bemcgarvey/ATSAME51J20Demo/firmware/CDC/firmware/src/app.c

#include "app.h"
#include <string.h>

// *****************************************************************************
// *****************************************************************************
// Section: Global Data Definitions
// *****************************************************************************
// *****************************************************************************

uint8_t CACHE_ALIGN cdcReadBuffer[APP_READ_BUFFER_SIZE];
uint8_t CACHE_ALIGN cdcWriteBuffer[APP_READ_BUFFER_SIZE];


// *****************************************************************************
/* Application Data

  Summary:
    Holds application data

  Description:
    This structure holds the application's data.

  Remarks:
    This structure should be initialized by the APP_Initialize function.
    
    Application strings and buffers are be defined outside this structure.
 */

APP_DATA appData;


// *****************************************************************************
// *****************************************************************************
// Section: Application Callback Functions
// *****************************************************************************
// *****************************************************************************

/*******************************************************
 * USB CDC Device Events - Application Event Handler
 *******************************************************/

USB_DEVICE_CDC_EVENT_RESPONSE APP_USBDeviceCDCEventHandler
(
        USB_DEVICE_CDC_INDEX index,
        USB_DEVICE_CDC_EVENT event,
        void * pData,
        uintptr_t userData
        ) {
    APP_DATA * appDataObject;
    USB_CDC_CONTROL_LINE_STATE * controlLineStateData;
    USB_DEVICE_CDC_EVENT_DATA_READ_COMPLETE * eventDataRead;

    appDataObject = (APP_DATA *) userData;

    switch (event) {
        case USB_DEVICE_CDC_EVENT_GET_LINE_CODING:

            /* This means the host wants to know the current line
             * coding. This is a control transfer request. Use the
             * USB_DEVICE_ControlSend() function to send the data to
             * host.  */

            USB_DEVICE_ControlSend(appDataObject->deviceHandle,
                    &appDataObject->getLineCodingData, sizeof (USB_CDC_LINE_CODING));

            break;

        case USB_DEVICE_CDC_EVENT_SET_LINE_CODING:

            /* This means the host wants to set the line coding.
             * This is a control transfer request. Use the
             * USB_DEVICE_ControlReceive() function to receive the
             * data from the host */

            USB_DEVICE_ControlReceive(appDataObject->deviceHandle,
                    &appDataObject->setLineCodingData, sizeof (USB_CDC_LINE_CODING));

            break;

        case USB_DEVICE_CDC_EVENT_SET_CONTROL_LINE_STATE:

            /* This means the host is setting the control line state.
             * Read the control line state. We will accept this request
             * for now. */

            controlLineStateData = (USB_CDC_CONTROL_LINE_STATE *) pData;
            appDataObject->controlLineStateData.dtr = controlLineStateData->dtr;
            appDataObject->controlLineStateData.carrier = controlLineStateData->carrier;

            USB_DEVICE_ControlStatus(appDataObject->deviceHandle, USB_DEVICE_CONTROL_STATUS_OK);

            break;

        case USB_DEVICE_CDC_EVENT_SEND_BREAK:

            /* This means that the host is requesting that a break of the
             * specified duration be sent. Read the break duration */

            appDataObject->breakData = ((USB_DEVICE_CDC_EVENT_DATA_SEND_BREAK *) pData)->breakDuration;

            /* Complete the control transfer by sending a ZLP  */
            USB_DEVICE_ControlStatus(appDataObject->deviceHandle, USB_DEVICE_CONTROL_STATUS_OK);

            break;

        case USB_DEVICE_CDC_EVENT_READ_COMPLETE:

            /* This means that the host has sent some data*/
            eventDataRead = (USB_DEVICE_CDC_EVENT_DATA_READ_COMPLETE *) pData;

            if (eventDataRead->status != USB_DEVICE_CDC_RESULT_ERROR) {
                appDataObject->isReadComplete = true;

                appDataObject->numBytesRead = eventDataRead->length;
            }
            break;

        case USB_DEVICE_CDC_EVENT_CONTROL_TRANSFER_DATA_RECEIVED:

            /* The data stage of the last control transfer is
             * complete. For now we accept all the data */

            USB_DEVICE_ControlStatus(appDataObject->deviceHandle, USB_DEVICE_CONTROL_STATUS_OK);
            break;

        case USB_DEVICE_CDC_EVENT_CONTROL_TRANSFER_DATA_SENT:

            /* This means the GET LINE CODING function data is valid. We don't
             * do much with this data in this demo. */
            break;

        case USB_DEVICE_CDC_EVENT_WRITE_COMPLETE:

            /* This means that the data write got completed. We can schedule
             * the next read. */

            appDataObject->isWriteComplete = true;
            break;

        default:
            break;
    }

    return USB_DEVICE_CDC_EVENT_RESPONSE_NONE;
}

/***********************************************
 * Application USB Device Layer Event Handler.
 ***********************************************/
void APP_USBDeviceEventHandler
(
        USB_DEVICE_EVENT event,
        void * eventData,
        uintptr_t context
        ) {
    USB_DEVICE_EVENT_DATA_CONFIGURED *configuredEventData;

    switch (event) {
        case USB_DEVICE_EVENT_SOF:

            /* This event is used for switch debounce. This flag is reset
             * by the switch process routine. */
            appData.sofEventHasOccurred = true;

            break;

        case USB_DEVICE_EVENT_RESET:

            /* Update LED to show reset state */
            LED_Off();

            appData.isConfigured = false;

            break;

        case USB_DEVICE_EVENT_CONFIGURED:

            /* Check the configuration. We only support configuration 1 */
            configuredEventData = (USB_DEVICE_EVENT_DATA_CONFIGURED*) eventData;

            if (configuredEventData->configurationValue == 1) {
                /* Update LED to show configured state */
                LED_On();

                /* Register the CDC Device application event handler here.
                 * Note how the appData object pointer is passed as the
                 * user data */

                USB_DEVICE_CDC_EventHandlerSet(USB_DEVICE_CDC_INDEX_0, APP_USBDeviceCDCEventHandler, (uintptr_t) & appData);

                /* Mark that the device is now configured */
                appData.isConfigured = true;
            }

            break;

        case USB_DEVICE_EVENT_POWER_DETECTED:

            /* VBUS was detected. We can attach the device */
            USB_DEVICE_Attach(appData.deviceHandle);

            break;

        case USB_DEVICE_EVENT_POWER_REMOVED:

            /* VBUS is not available. We can detach the device */
            USB_DEVICE_Detach(appData.deviceHandle);

            appData.isConfigured = false;

            LED_Off();

            break;

        case USB_DEVICE_EVENT_SUSPENDED:

            /* Switch LED to show suspended state */
            LED_Off();

            break;

        case USB_DEVICE_EVENT_RESUMED:
        case USB_DEVICE_EVENT_ERROR:
        default:

            break;
    }
}

// *****************************************************************************
// *****************************************************************************
// Section: Application Local Functions
// *****************************************************************************
// *****************************************************************************

/*****************************************************
 * This function is called in every step of the
 * application state machine.
 *****************************************************/

bool APP_StateReset(void) {
    /* This function returns true if the device
     * was reset  */

    bool retVal;

    if (appData.isConfigured == false) {
        appData.state = APP_STATE_WAIT_FOR_CONFIGURATION;
        appData.readTransferHandle = USB_DEVICE_CDC_TRANSFER_HANDLE_INVALID;
        appData.writeTransferHandle = USB_DEVICE_CDC_TRANSFER_HANDLE_INVALID;
        appData.isReadComplete = true;
        appData.isWriteComplete = true;
        retVal = true;
    } else {
        retVal = false;
    }

    return (retVal);
}

// *****************************************************************************
// *****************************************************************************
// Section: Application Initialization and State Machine Functions
// *****************************************************************************
// *****************************************************************************

/*******************************************************************************
  Function:
    void APP_Initialize(void)

  Remarks:
    See prototype in app.h.
 */

void APP_Initialize(void) {
    /* Place the App state machine in its initial state. */
    appData.state = APP_STATE_INIT;

    /* Device Layer Handle  */
    appData.deviceHandle = USB_DEVICE_HANDLE_INVALID;

    /* Device configured status */
    appData.isConfigured = false;

    /* Initial get line coding state */
    appData.getLineCodingData.dwDTERate = 9600;
    appData.getLineCodingData.bParityType = 0;
    appData.getLineCodingData.bParityType = 0;
    appData.getLineCodingData.bDataBits = 8;

    /* Read Transfer Handle */
    appData.readTransferHandle = USB_DEVICE_CDC_TRANSFER_HANDLE_INVALID;

    /* Write Transfer Handle */
    appData.writeTransferHandle = USB_DEVICE_CDC_TRANSFER_HANDLE_INVALID;

    /* Initialize the read complete flag */
    appData.isReadComplete = true;

    /*Initialize the write complete flag*/
    appData.isWriteComplete = true;

    /* Reset other flags */
    appData.sofEventHasOccurred = false;

    /* Set up the read buffer */
    appData.cdcReadBuffer = &cdcReadBuffer[0];

    /* Set up the read buffer */
    appData.cdcWriteBuffer = &cdcWriteBuffer[0];
}

/******************************************************************************
  Function:
    void APP_Tasks(void)

  Remarks:
    See prototype in app.h.
 */

void APP_Tasks(void) {
    /* Update the application state machine based
     * on the current state */

    switch (appData.state) {
        case APP_STATE_INIT:

            /* Open the device layer */
            appData.deviceHandle = USB_DEVICE_Open(USB_DEVICE_INDEX_0, DRV_IO_INTENT_READWRITE);

            if (appData.deviceHandle != USB_DEVICE_HANDLE_INVALID) {
                /* Register a callback with device layer to get event notification (for end point 0) */
                USB_DEVICE_EventHandlerSet(appData.deviceHandle, APP_USBDeviceEventHandler, 0);

                appData.state = APP_STATE_WAIT_FOR_CONFIGURATION;
            } else {
                /* The Device Layer is not ready to be opened. We should try
                 * again later. */
            }

            break;

        case APP_STATE_WAIT_FOR_CONFIGURATION:

            /* Check if the device was configured */
            if (appData.isConfigured) {
                /* If the device is configured then lets start reading */
                appData.state = APP_STATE_SCHEDULE_READ;
            }

            break;

        case APP_STATE_SCHEDULE_READ:

            if (APP_StateReset()) {
                break;
            }

            /* If a read is complete, then schedule a read
             * else wait for the current read to complete */

            appData.state = APP_STATE_WAIT_FOR_READ_COMPLETE;
            if (appData.isReadComplete == true) {
                appData.isReadComplete = false;
                appData.readTransferHandle = USB_DEVICE_CDC_TRANSFER_HANDLE_INVALID;

                USB_DEVICE_CDC_Read(USB_DEVICE_CDC_INDEX_0,
                        &appData.readTransferHandle, appData.cdcReadBuffer,
                        APP_READ_BUFFER_SIZE);

                if (appData.readTransferHandle == USB_DEVICE_CDC_TRANSFER_HANDLE_INVALID) {
                    appData.state = APP_STATE_ERROR;
                    break;
                }
            }

            break;

        case APP_STATE_WAIT_FOR_READ_COMPLETE:
            if (APP_StateReset()) {
                break;
            }
            if (appData.isReadComplete) {
                for (int i = 0; i < appData.numBytesRead; ++i) {
                    while (appData.isWriteComplete == false) {
                        vTaskDelay(1);
                    }
                    appData.numBytesToWrite = 0;
                    switch (appData.cdcReadBuffer[i]) {
                        case '1': BlueLed_Toggle();
                            break;
                        case '2': GreenLed_Set();
                            strcpy((char *) appData.cdcWriteBuffer, "Green On\r\n");
                            appData.numBytesToWrite = strlen((char *) appData.cdcWriteBuffer);
                            break;
                        case '3': GreenLed_Clear();
                            strcpy((char *) appData.cdcWriteBuffer, "Green Off\r\n");
                            appData.numBytesToWrite = strlen((char *) appData.cdcWriteBuffer);
                            break;
                        case '4':
                            for (int j = 0; j < 26 * 4; ++j) {
                                appData.cdcWriteBuffer[j] = 'a' + (j % 26);
                            }
                            appData.cdcWriteBuffer[26 * 4] = '\r';
                            appData.cdcWriteBuffer[26 * 4 + 1] = '\n';
                            appData.cdcWriteBuffer[26 * 4 + 2] = '\0';
                            appData.numBytesToWrite = strlen((char *) appData.cdcWriteBuffer);
                            break;
                    }
                    if (appData.numBytesToWrite > 0) {
                        appData.writeTransferHandle = USB_DEVICE_CDC_TRANSFER_HANDLE_INVALID;
                        appData.isWriteComplete = false;
                        appData.state = APP_STATE_WAIT_FOR_WRITE_COMPLETE;
                        USB_DEVICE_CDC_Write(USB_DEVICE_CDC_INDEX_0,
                                &appData.writeTransferHandle,
                                appData.cdcWriteBuffer, appData.numBytesToWrite,
                                USB_DEVICE_CDC_TRANSFER_FLAGS_DATA_COMPLETE);
                    }
                }
                appData.state = APP_STATE_SCHEDULE_READ;
            }
            break;
        case APP_STATE_SCHEDULE_WRITE:

            if (APP_StateReset()) {
                break;
            }
            /* Setup the write */
            appData.writeTransferHandle = USB_DEVICE_CDC_TRANSFER_HANDLE_INVALID;
            appData.isWriteComplete = false;
            appData.state = APP_STATE_WAIT_FOR_WRITE_COMPLETE;
            USB_DEVICE_CDC_Write(USB_DEVICE_CDC_INDEX_0,
                    &appData.writeTransferHandle,
                    appData.cdcWriteBuffer, appData.numBytesToWrite,
                    USB_DEVICE_CDC_TRANSFER_FLAGS_DATA_COMPLETE);
            break;
        case APP_STATE_WAIT_FOR_WRITE_COMPLETE:
            if (APP_StateReset()) {
                break;
            }
            if (appData.isWriteComplete == true) {
                appData.state = APP_STATE_SCHEDULE_READ;
            }
            break;
        case APP_STATE_ERROR:
        default:
            break;
    }
}

/*******************************************************************************
 End of File
 */
