bemcgarvey/ATSAME51J20Demo/firmware/CDC/firmware/src/config/default/initialization.c

/*******************************************************************************
  System Initialization File

  File Name:
    initialization.c

  Summary:
    This file contains source code necessary to initialize the system.

  Description:
    This file contains source code necessary to initialize the system.  It
    implements the "SYS_Initialize" function, defines the configuration bits,
    and allocates any necessary global system resources,
 *******************************************************************************/

// DOM-IGNORE-BEGIN
/*******************************************************************************
* Copyright (C) 2018 Microchip Technology Inc. and its subsidiaries.
*
* Subject to your compliance with these terms, you may use Microchip software
* and any derivatives exclusively with Microchip products. It is your
* responsibility to comply with third party license terms applicable to your
* use of third party software (including open source software) that may
* accompany Microchip software.
*
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
* IN NO EVENT WILL MICROCHIP BE LIABLE FOR ANY INDIRECT, SPECIAL, PUNITIVE,
* INCIDENTAL OR CONSEQUENTIAL LOSS, DAMAGE, COST OR EXPENSE OF ANY KIND
* WHATSOEVER RELATED TO THE SOFTWARE, HOWEVER CAUSED, EVEN IF MICROCHIP HAS
* BEEN ADVISED OF THE POSSIBILITY OR THE DAMAGES ARE FORESEEABLE. TO THE
* FULLEST EXTENT ALLOWED BY LAW, MICROCHIP'S TOTAL LIABILITY ON ALL CLAIMS IN
* ANY WAY RELATED TO THIS SOFTWARE WILL NOT EXCEED THE AMOUNT OF FEES, IF ANY,
* THAT YOU HAVE PAID DIRECTLY TO MICROCHIP FOR THIS SOFTWARE.
 *******************************************************************************/
// DOM-IGNORE-END

// *****************************************************************************
// *****************************************************************************
// Section: Included Files
// *****************************************************************************
// *****************************************************************************
#include "configuration.h"
#include "definitions.h"
#include "device.h"



// ****************************************************************************
// ****************************************************************************
// Section: Configuration Bits
// ****************************************************************************
// ****************************************************************************
#pragma config BOD33_DIS = SET
#pragma config BOD33USERLEVEL = 0x1c
#pragma config BOD33_ACTION = RESET
#pragma config BOD33_HYST = 0x2
#pragma config NVMCTRL_BOOTPROT = 0
#pragma config NVMCTRL_SEESBLK = 0x0
#pragma config NVMCTRL_SEEPSZ = 0x0
#pragma config RAMECC_ECCDIS = SET
#pragma config WDT_ENABLE = CLEAR
#pragma config WDT_ALWAYSON = CLEAR
#pragma config WDT_PER = CYC8192
#pragma config WDT_WINDOW = CYC8192
#pragma config WDT_EWOFFSET = CYC8192
#pragma config WDT_WEN = CLEAR
#pragma config NVMCTRL_REGION_LOCKS = 0xffffffff




// *****************************************************************************
// *****************************************************************************
// Section: Driver Initialization Data
// *****************************************************************************
// *****************************************************************************
// <editor-fold defaultstate="collapsed" desc="DRV_SDMMC Instance 0 Initialization Data">

/* SDMMC Client Objects Pool */
static DRV_SDMMC_CLIENT_OBJ drvSDMMC0ClientObjPool[DRV_SDMMC_CLIENTS_NUMBER_IDX0];

/* SDMMC Transfer Objects Pool */
static DRV_SDMMC_BUFFER_OBJ drvSDMMC0BufferObjPool[DRV_SDMMC_QUEUE_SIZE_IDX0];


const DRV_SDMMC_PLIB_API drvSDMMC0PlibAPI = {
    .sdhostCallbackRegister = (DRV_SDMMC_PLIB_CALLBACK_REGISTER)SDHC0_CallbackRegister,
    .sdhostInitModule = (DRV_SDMMC_PLIB_INIT_MODULE)SDHC0_ModuleInit,
    .sdhostSetClock  = (DRV_SDMMC_PLIB_SET_CLOCK)SDHC0_ClockSet,
    .sdhostIsCmdLineBusy = (DRV_SDMMC_PLIB_IS_CMD_LINE_BUSY)SDHC0_IsCmdLineBusy,
    .sdhostIsDatLineBusy = (DRV_SDMMC_PLIB_IS_DATA_LINE_BUSY)SDHC0_IsDatLineBusy,
    .sdhostSendCommand = (DRV_SDMMC_PLIB_SEND_COMMAND)SDHC0_CommandSend,
    .sdhostReadResponse = (DRV_SDMMC_PLIB_READ_RESPONSE)SDHC0_ResponseRead,
    .sdhostSetBlockCount = (DRV_SDMMC_PLIB_SET_BLOCK_COUNT)SDHC0_BlockCountSet,
    .sdhostSetBlockSize = (DRV_SDMMC_PLIB_SET_BLOCK_SIZE)SDHC0_BlockSizeSet,
    .sdhostSetBusWidth = (DRV_SDMMC_PLIB_SET_BUS_WIDTH)SDHC0_BusWidthSet,
    .sdhostSetSpeedMode = (DRV_SDMMC_PLIB_SET_SPEED_MODE)SDHC0_SpeedModeSet,
    .sdhostSetupDma = (DRV_SDMMC_PLIB_SETUP_DMA)SDHC0_DmaSetup,
    .sdhostGetCommandError = (DRV_SDMMC_PLIB_GET_COMMAND_ERROR)SDHC0_CommandErrorGet,
    .sdhostGetDataError = (DRV_SDMMC_PLIB_GET_DATA_ERROR)SDHC0_DataErrorGet,
    .sdhostClockEnable = (DRV_SDMMC_PLIB_CLOCK_ENABLE)SDHC0_ClockEnable,
    .sdhostResetError = (DRV_SDMMC_PLIB_RESET_ERROR)SDHC0_ErrorReset,
    .sdhostIsCardAttached = (DRV_SDMMC_PLIB_IS_CARD_ATTACHED)SDHC0_IsCardAttached,
    .sdhostIsWriteProtected = (DRV_SDMMC_PLIB_IS_WRITE_PROTECTED)NULL,
};

/*** SDMMC Driver Initialization Data ***/
const DRV_SDMMC_INIT drvSDMMC0InitData =
{
    .sdmmcPlib                      = &drvSDMMC0PlibAPI,
    .bufferObjPool                  = (uintptr_t)&drvSDMMC0BufferObjPool[0],
    .bufferObjPoolSize              = DRV_SDMMC_QUEUE_SIZE_IDX0,
    .clientObjPool                  = (uintptr_t)&drvSDMMC0ClientObjPool[0],
    .numClients                     = DRV_SDMMC_CLIENTS_NUMBER_IDX0,
    .protocol                       = DRV_SDMMC_PROTOCOL_SUPPORT_IDX0,
    .cardDetectionMethod            = DRV_SDMMC_CARD_DETECTION_METHOD_IDX0,
    .cardDetectionPollingIntervalMs = 0,
    .isWriteProtectCheckEnabled     = false,
    .speedMode                      = DRV_SDMMC_CONFIG_SPEED_MODE_IDX0,
    .busWidth                       = DRV_SDMMC_CONFIG_BUS_WIDTH_IDX0,
	.sleepWhenIdle 					= false,
    .isFsEnabled                    = false,
};

// </editor-fold>



// *****************************************************************************
// *****************************************************************************
// Section: System Data
// *****************************************************************************
// *****************************************************************************
/* Structure to hold the object handles for the modules in the system. */
SYSTEM_OBJECTS sysObj;

// *****************************************************************************
// *****************************************************************************
// Section: Library/Stack Initialization Data
// *****************************************************************************
// *****************************************************************************
/******************************************************
 * USB Driver Initialization
 ******************************************************/
 
/*  When designing a Self-powered USB Device, the application should make sure
    that USB_DEVICE_Attach() function is called only when VBUS is actively powered.
	Therefore, the firmware needs some means to detect when the Host is powering 
	the VBUS. A 5V tolerant I/O pin can be connected to VBUS (through a resistor)
	and can be used to detect when VBUS is high or low. The application can specify
	a VBUS Detect function through the USB Driver Initialize data structure. 
	The USB device stack will periodically call this function. If the VBUS is 
	detected, the USB_DEVICE_EVENT_POWER_DETECTED event is generated. If the VBUS 
	is removed (i.e., the device is physically detached from Host), the USB stack 
	will generate the event USB_DEVICE_EVENT_POWER_REMOVED. The application should 
	call USB_DEVICE_Detach() when VBUS is removed. 
    
    The following are the steps to generate the VBUS_SENSE Function through MHC     
        1) Navigate to MHC->Tools->Pin Configuration and Configure the pin used 
		   as VBUS_SENSE. Set this pin Function as "GPIO" and set as "Input". 
		   Provide a custom name to the pin.
        2) Select the USB Driver Component in MHC Project Graph and enable the  
		   "Enable VBUS Sense" Check-box.     
        3) Specify the custom name of the VBUS SENSE pin in the "VBUS SENSE Pin Name" box.  */ 
static DRV_USB_VBUS_LEVEL DRV_USBFSV1_VBUS_Comparator(void)
{
    DRV_USB_VBUS_LEVEL retVal = DRV_USB_VBUS_LEVEL_INVALID;
    
    if(true == USB_VBUS_SENSE_Get())
    {
        retVal = DRV_USB_VBUS_LEVEL_VALID;
    }
	return (retVal);

}


const DRV_USBFSV1_INIT drvUSBInit =
{
	/* Interrupt Source for USB module */
	.interruptSource = USB_OTHER_IRQn,
 
	/* Interrupt Source for USB module */
	.interruptSource1 = USB_SOF_HSOF_IRQn,
 
	/* Interrupt Source for USB module */
	.interruptSource2 = USB_TRCPT0_IRQn,
 
	/* Interrupt Source for USB module */
	.interruptSource3 = USB_TRCPT1_IRQn,

    /* System module initialization */
    .moduleInit = {0},

    /* USB Controller to operate as USB Device */
    .operationMode = DRV_USBFSV1_OPMODE_DEVICE,

    /* USB Full Speed Operation */
	.operationSpeed = USB_SPEED_FULL,
    
    /* Stop in idle */
    .runInStandby = true,

    /* Suspend in sleep */
    .suspendInSleep = false,

    /* Identifies peripheral (PLIB-level) ID */
    .usbID = USB_REGS,
	
    /* Function to check for VBus */
    .vbusComparator = DRV_USBFSV1_VBUS_Comparator
	
};




// *****************************************************************************
// *****************************************************************************
// Section: System Initialization
// *****************************************************************************
// *****************************************************************************
// <editor-fold defaultstate="collapsed" desc="SYS_TIME Initialization Data">

const SYS_TIME_PLIB_INTERFACE sysTimePlibAPI = {
    .timerCallbackSet = (SYS_TIME_PLIB_CALLBACK_REGISTER)TC0_TimerCallbackRegister,
    .timerStart = (SYS_TIME_PLIB_START)TC0_TimerStart,
    .timerStop = (SYS_TIME_PLIB_STOP)TC0_TimerStop,
    .timerFrequencyGet = (SYS_TIME_PLIB_FREQUENCY_GET)TC0_TimerFrequencyGet,
    .timerPeriodSet = (SYS_TIME_PLIB_PERIOD_SET)TC0_Timer16bitPeriodSet,
    .timerCompareSet = (SYS_TIME_PLIB_COMPARE_SET)TC0_Timer16bitCompareSet,
    .timerCounterGet = (SYS_TIME_PLIB_COUNTER_GET)TC0_Timer16bitCounterGet,
};

const SYS_TIME_INIT sysTimeInitData =
{
    .timePlib = &sysTimePlibAPI,
    .hwTimerIntNum = TC0_IRQn,
};

// </editor-fold>



// *****************************************************************************
// *****************************************************************************
// Section: Local initialization functions
// *****************************************************************************
// *****************************************************************************



/*******************************************************************************
  Function:
    void SYS_Initialize ( void *data )

  Summary:
    Initializes the board, services, drivers, application and other modules.

  Remarks:
 */

void SYS_Initialize ( void* data )
{

    NVMCTRL_Initialize( );

  
    PORT_Initialize();

    CLOCK_Initialize();




    EVSYS_Initialize();

    TC0_TimerInitialize();

	SDHC0_Initialize();



    sysObj.drvSDMMC0 = DRV_SDMMC_Initialize(DRV_SDMMC_INDEX_0,(SYS_MODULE_INIT *)&drvSDMMC0InitData);


    sysObj.sysTime = SYS_TIME_Initialize(SYS_TIME_INDEX_0, (SYS_MODULE_INIT *)&sysTimeInitData);


	 /* Initialize the USB device layer */
    sysObj.usbDevObject0 = USB_DEVICE_Initialize (USB_DEVICE_INDEX_0 , ( SYS_MODULE_INIT* ) & usbDevInitData);
	
	

	/* Initialize USB Driver */ 
    sysObj.drvUSBFSV1Object = DRV_USBFSV1_Initialize(DRV_USBFSV1_INDEX_0, (SYS_MODULE_INIT *) &drvUSBInit);	


    APP_Initialize();


    NVIC_Initialize();

}


/*******************************************************************************
 End of File
*/
