bemcgarvey/ATSAME51J20Demo/firmware/Demo/firmware/src/config/default/peripheral/sercom/i2c_master/plib_sercom1_i2c_master.c

/*******************************************************************************
  Serial Communication Interface Inter-Integrated Circuit (SERCOM I2C) Library
  Source File

  Company:
    Microchip Technology Inc.

  File Name:
    plib_sercom1_i2c.c

  Summary:
    SERCOM I2C PLIB Implementation file

  Description:
    This file defines the interface to the SERCOM I2C peripheral library.
    This library provides access to and control of the associated peripheral
    instance.

*******************************************************************************/
// DOM-IGNORE-BEGIN
/*******************************************************************************
* Copyright (C) 2018 Microchip Technology Inc. and its subsidiaries.
*
* Subject to your compliance with these terms, you may use Microchip software
* and any derivatives exclusively with Microchip products. It is your
* responsibility to comply with third party license terms applicable to your
* use of third party software (including open source software) that may
* accompany Microchip software.
*
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
* IN NO EVENT WILL MICROCHIP BE LIABLE FOR ANY INDIRECT, SPECIAL, PUNITIVE,
* INCIDENTAL OR CONSEQUENTIAL LOSS, DAMAGE, COST OR EXPENSE OF ANY KIND
* WHATSOEVER RELATED TO THE SOFTWARE, HOWEVER CAUSED, EVEN IF MICROCHIP HAS
* BEEN ADVISED OF THE POSSIBILITY OR THE DAMAGES ARE FORESEEABLE. TO THE
* FULLEST EXTENT ALLOWED BY LAW, MICROCHIP'S TOTAL LIABILITY ON ALL CLAIMS IN
* ANY WAY RELATED TO THIS SOFTWARE WILL NOT EXCEED THE AMOUNT OF FEES, IF ANY,
* THAT YOU HAVE PAID DIRECTLY TO MICROCHIP FOR THIS SOFTWARE.
*******************************************************************************/
// DOM-IGNORE-END

// *****************************************************************************
// *****************************************************************************
// Section: Included Files
// *****************************************************************************
// *****************************************************************************

#include "interrupts.h"
#include "plib_sercom1_i2c_master.h"


// *****************************************************************************
// *****************************************************************************
// Section: Global Data
// *****************************************************************************
// *****************************************************************************


#define SERCOM1_I2CM_SPEED_HZ           100000

/* SERCOM1 I2C baud value */
#define SERCOM1_I2CM_BAUD_VALUE         (0xFFU)


static SERCOM_I2C_OBJ sercom1I2CObj;

// *****************************************************************************
// *****************************************************************************
// Section: SERCOM1 I2C Implementation
// *****************************************************************************
// *****************************************************************************
// *****************************************************************************

void SERCOM1_I2C_Initialize(void)
{
    /* Reset the module */
    SERCOM1_REGS->I2CM.SERCOM_CTRLA = SERCOM_I2CM_CTRLA_SWRST_Msk ;

    /* Wait for synchronization */
    while((SERCOM1_REGS->I2CM.SERCOM_SYNCBUSY) != 0U)
    {
        /* Do nothing */
    }

    /* Enable smart mode */
    SERCOM1_REGS->I2CM.SERCOM_CTRLB = SERCOM_I2CM_CTRLB_SMEN_Msk;

    /* Wait for synchronization */
    while((SERCOM1_REGS->I2CM.SERCOM_SYNCBUSY) != 0U)
    {
        /* Do nothing */
    }

    /* Baud rate - Master Baud Rate*/
    SERCOM1_REGS->I2CM.SERCOM_BAUD = SERCOM1_I2CM_BAUD_VALUE;

    /* Set Operation Mode (Master), SDA Hold time, run in stand by and i2c master enable */
    SERCOM1_REGS->I2CM.SERCOM_CTRLA = SERCOM_I2CM_CTRLA_MODE_I2C_MASTER | SERCOM_I2CM_CTRLA_SDAHOLD_75NS | SERCOM_I2CM_CTRLA_SPEED_STANDARD_AND_FAST_MODE | SERCOM_I2CM_CTRLA_SCLSM(0UL) | SERCOM_I2CM_CTRLA_ENABLE_Msk ;

    /* Wait for synchronization */
    while((SERCOM1_REGS->I2CM.SERCOM_SYNCBUSY) != 0U)
    {
        /* Do nothing */
    }

    /* Initial Bus State: IDLE */
    SERCOM1_REGS->I2CM.SERCOM_STATUS = (uint16_t)SERCOM_I2CM_STATUS_BUSSTATE(0x01UL);

    /* Wait for synchronization */
    while((SERCOM1_REGS->I2CM.SERCOM_SYNCBUSY) != 0U)
    {
        /* Do nothing */
    }

    /* Initialize the SERCOM1 PLib Object */
    sercom1I2CObj.error = SERCOM_I2C_ERROR_NONE;
    sercom1I2CObj.state = SERCOM_I2C_STATE_IDLE;

    /* Enable all Interrupts */
    SERCOM1_REGS->I2CM.SERCOM_INTENSET = (uint8_t)SERCOM_I2CM_INTENSET_Msk;
}

static bool SERCOM1_I2C_CalculateBaudValue(uint32_t srcClkFreq, uint32_t i2cClkSpeed, uint32_t* baudVal)
{
    uint32_t baudValue = 0U;
    float fSrcClkFreq = (float)srcClkFreq;
    float fI2cClkSpeed = (float)i2cClkSpeed;
    float fBaudValue = 0.0f;

    /* Reference clock frequency must be atleast two times the baud rate */
    if (srcClkFreq < (2U * i2cClkSpeed))
    {
        return false;
    }

    if (i2cClkSpeed <= 1000000U)
    {
        /* Standard, FM and FM+ baud calculation */
        fBaudValue = (fSrcClkFreq / fI2cClkSpeed) - ((fSrcClkFreq * (100.0f / 1000000000.0f)) + 10.0f);
        baudValue = (uint32_t)fBaudValue;
    }
    else
    {
        return false;
    }
    if (i2cClkSpeed <= 400000U)
    {
        /* For I2C clock speed upto 400 kHz, the value of BAUD<7:0> determines both SCL_L and SCL_H with SCL_L = SCL_H */
        if (baudValue > (0xFFU * 2U))
        {
            /* Set baud rate to the minimum possible value */
            baudValue = 0xFFU;
        }
        else if (baudValue <= 1U)
        {
            /* Baud value cannot be 0. Set baud rate to maximum possible value */
            baudValue = 1U;
        }
        else
        {
            baudValue /= 2U;
        }
    }
    else
    {
        /* To maintain the ratio of SCL_L:SCL_H to 2:1, the max value of BAUD_LOW<15:8>:BAUD<7:0> can be 0xFF:0x7F. Hence BAUD_LOW + BAUD can not exceed 255+127 = 382 */
        if (baudValue >= 382U)
        {
            /* Set baud rate to the minimum possible value while maintaining SCL_L:SCL_H to 2:1 */
            baudValue = (0xFFUL << 8U) | (0x7FU);
        }
        else if (baudValue <= 3U)
        {
            /* Baud value cannot be 0. Set baud rate to maximum possible value while maintaining SCL_L:SCL_H to 2:1 */
            baudValue = (2UL << 8U) | 1U;
        }
        else
        {
            /* For Fm+ mode, I2C SCL_L:SCL_H to 2:1 */
            baudValue  = ((((baudValue * 2U)/3U) << 8U) | (baudValue/3U));
        }
    }
    *baudVal = baudValue;
    return true;
}

bool SERCOM1_I2C_TransferSetup(SERCOM_I2C_TRANSFER_SETUP* setup, uint32_t srcClkFreq )
{
    uint32_t baudValue;
    uint32_t i2cClkSpeed;
    uint32_t i2cSpeedMode = 0;

    if (setup == NULL)
    {
        return false;
    }

    i2cClkSpeed = setup->clkSpeed;

    if( srcClkFreq == 0U)
    {
        srcClkFreq = 60000000UL;
    }

    if (SERCOM1_I2C_CalculateBaudValue(srcClkFreq, i2cClkSpeed, &baudValue) == false)
    {
        return false;
    }

    if (i2cClkSpeed > 400000U)
    {
        i2cSpeedMode = 1U;
    }

    /* Disable the I2C before changing the I2C clock speed */
    SERCOM1_REGS->I2CM.SERCOM_CTRLA &= ~SERCOM_I2CM_CTRLA_ENABLE_Msk;

    /* Wait for synchronization */
    while((SERCOM1_REGS->I2CM.SERCOM_SYNCBUSY) != 0U)
    {
        /* Do nothing */
    }


    /* Baud rate - Master Baud Rate*/
    SERCOM1_REGS->I2CM.SERCOM_BAUD = baudValue;

    SERCOM1_REGS->I2CM.SERCOM_CTRLA  = ((SERCOM1_REGS->I2CM.SERCOM_CTRLA & ~SERCOM_I2CM_CTRLA_SPEED_Msk) | (SERCOM_I2CM_CTRLA_SPEED(i2cSpeedMode)));

    /* Re-enable the I2C module */
    SERCOM1_REGS->I2CM.SERCOM_CTRLA |= SERCOM_I2CM_CTRLA_ENABLE_Msk;

    /* Wait for synchronization */
    while((SERCOM1_REGS->I2CM.SERCOM_SYNCBUSY) != 0U)
    {
        /* Do nothing */
    }


    /* Since the I2C module was disabled, re-initialize the bus state to IDLE */
    SERCOM1_REGS->I2CM.SERCOM_STATUS = (uint16_t)SERCOM_I2CM_STATUS_BUSSTATE(0x01UL);

    /* Wait for synchronization */
    while((SERCOM1_REGS->I2CM.SERCOM_SYNCBUSY) != 0U)
    {
        /* Do nothing */
    }

    return true;
}

void SERCOM1_I2C_CallbackRegister(SERCOM_I2C_CALLBACK callback, uintptr_t contextHandle)
{
    sercom1I2CObj.callback = callback;

    sercom1I2CObj.context  = contextHandle;
}


static void SERCOM1_I2C_SendAddress(uint16_t address, bool dir)
{
    /* If operation is I2C read */
    if(dir)
    {
        /* <xxxx-xxxR> <read-data> <P> */

        /* Next state will be to read data */
        sercom1I2CObj.state = SERCOM_I2C_STATE_TRANSFER_READ;
    }
    else
    {
        /* <xxxx-xxxW> <write-data> <P> */

        /* Next state will be to write data */
        sercom1I2CObj.state = SERCOM_I2C_STATE_TRANSFER_WRITE;
    }


    SERCOM1_REGS->I2CM.SERCOM_ADDR = ((uint32_t)address << 1U) | (dir ? 1UL :0UL);

    /* Wait for synchronization */
    while((SERCOM1_REGS->I2CM.SERCOM_SYNCBUSY) != 0U)
    {
        /* Do nothing */
    }

}

static void SERCOM1_I2C_InitiateTransfer(uint16_t address, bool dir)
{
    sercom1I2CObj.writeCount = 0U;
    sercom1I2CObj.readCount = 0U;

    /* Clear all flags */
    SERCOM1_REGS->I2CM.SERCOM_INTFLAG = (uint8_t)SERCOM_I2CM_INTFLAG_Msk;

    /* Smart mode enabled with SCLSM = 0, - ACK is set to send while receiving the data */
    SERCOM1_REGS->I2CM.SERCOM_CTRLB &= ~SERCOM_I2CM_CTRLB_ACKACT_Msk;

    /* Wait for synchronization */
    while((SERCOM1_REGS->I2CM.SERCOM_SYNCBUSY) != 0U)
    {
        /* Do nothing */
    }


    SERCOM1_I2C_SendAddress(address, dir);
}

static bool SERCOM1_I2C_XferSetup(
    uint16_t address,
    uint8_t* wrData,
    uint32_t wrLength,
    uint8_t* rdData,
    uint32_t rdLength,
    bool dir,
    bool isHighSpeed
)
{
    /* Check for ongoing transfer */
    if(sercom1I2CObj.state != SERCOM_I2C_STATE_IDLE)
    {
        return false;
    }

    sercom1I2CObj.address        = address;
    sercom1I2CObj.readBuffer     = rdData;
    sercom1I2CObj.readSize       = rdLength;
    sercom1I2CObj.writeBuffer    = wrData;
    sercom1I2CObj.writeSize      = wrLength;
    sercom1I2CObj.transferDir    = dir;
    sercom1I2CObj.isHighSpeed    = isHighSpeed;
    sercom1I2CObj.error          = SERCOM_I2C_ERROR_NONE;


    SERCOM1_I2C_InitiateTransfer(address, dir);

    return true;
}

bool SERCOM1_I2C_Read(uint16_t address, uint8_t* rdData, uint32_t rdLength)
{
    return SERCOM1_I2C_XferSetup(address, NULL, 0, rdData, rdLength, true, false);
}

bool SERCOM1_I2C_Write(uint16_t address, uint8_t* wrData, uint32_t wrLength)
{
    return SERCOM1_I2C_XferSetup(address, wrData, wrLength, NULL, 0, false, false);
}

bool SERCOM1_I2C_WriteRead(uint16_t address, uint8_t* wrData, uint32_t wrLength, uint8_t* rdData, uint32_t rdLength)
{
    return SERCOM1_I2C_XferSetup(address, wrData, wrLength, rdData, rdLength, false, false);
}


bool SERCOM1_I2C_IsBusy(void)
{
    bool isBusy = true;
    if((sercom1I2CObj.state == SERCOM_I2C_STATE_IDLE))
    {
        if(((SERCOM1_REGS->I2CM.SERCOM_STATUS & SERCOM_I2CM_STATUS_BUSSTATE_Msk) == SERCOM_I2CM_STATUS_BUSSTATE(0x01UL)))
        {
           isBusy = false;
        }
    }
    return isBusy;
}

SERCOM_I2C_ERROR SERCOM1_I2C_ErrorGet(void)
{
    return sercom1I2CObj.error;
}

void SERCOM1_I2C_InterruptHandler(void)
{
    if(SERCOM1_REGS->I2CM.SERCOM_INTENSET != 0U)
    {
        /* Checks if the arbitration lost in multi-master scenario */
        if((SERCOM1_REGS->I2CM.SERCOM_STATUS & SERCOM_I2CM_STATUS_ARBLOST_Msk) == SERCOM_I2CM_STATUS_ARBLOST_Msk)
        {
            /* Set Error status */
            sercom1I2CObj.state = SERCOM_I2C_STATE_ERROR;
            sercom1I2CObj.error = SERCOM_I2C_ERROR_BUS;

        }
        /* Check for Bus Error during transmission */
        else if((SERCOM1_REGS->I2CM.SERCOM_STATUS & SERCOM_I2CM_STATUS_BUSERR_Msk) == SERCOM_I2CM_STATUS_BUSERR_Msk)
        {
            /* Set Error status */
            sercom1I2CObj.state = SERCOM_I2C_STATE_ERROR;
            sercom1I2CObj.error = SERCOM_I2C_ERROR_BUS;
        }
        /* Checks slave acknowledge for address or data */
        else if((SERCOM1_REGS->I2CM.SERCOM_STATUS & SERCOM_I2CM_STATUS_RXNACK_Msk) == SERCOM_I2CM_STATUS_RXNACK_Msk)
        {
            sercom1I2CObj.state = SERCOM_I2C_STATE_ERROR;
            sercom1I2CObj.error = SERCOM_I2C_ERROR_NAK;
        }
        else
        {
            switch(sercom1I2CObj.state)
            {
                case SERCOM_I2C_REINITIATE_TRANSFER:

                    if (sercom1I2CObj.writeSize != 0U)
                    {
                        /* Initiate Write transfer */
                        SERCOM1_I2C_InitiateTransfer(sercom1I2CObj.address, false);
                    }
                    else
                    {
                        /* Initiate Read transfer */
                        SERCOM1_I2C_InitiateTransfer(sercom1I2CObj.address, true);
                    }

                    break;


                case SERCOM_I2C_STATE_IDLE:

                    break;



                case SERCOM_I2C_STATE_TRANSFER_WRITE:

                    if (sercom1I2CObj.writeCount == (sercom1I2CObj.writeSize))
                    {
                        if(sercom1I2CObj.readSize != 0U)
                        {

                            /* Write 7bit address with direction (ADDR.ADDR[0]) equal to 1*/
                            SERCOM1_REGS->I2CM.SERCOM_ADDR =  ((uint32_t)(sercom1I2CObj.address) << 1U) | (uint32_t)I2C_TRANSFER_READ;

                            /* Wait for synchronization */
                            while((SERCOM1_REGS->I2CM.SERCOM_SYNCBUSY) != 0U)
                            {
                                /* Do nothing */
                            }

                            sercom1I2CObj.state = SERCOM_I2C_STATE_TRANSFER_READ;

                        }
                        else
                        {
                            SERCOM1_REGS->I2CM.SERCOM_CTRLB |= SERCOM_I2CM_CTRLB_CMD(3UL);

                            /* Wait for synchronization */
                            while((SERCOM1_REGS->I2CM.SERCOM_SYNCBUSY) != 0U)
                            {
                                /* Do nothing */
                            }


                            sercom1I2CObj.state = SERCOM_I2C_STATE_TRANSFER_DONE;
                        }
                    }
                    /* Write next byte */
                    else
                    {
                        SERCOM1_REGS->I2CM.SERCOM_DATA = sercom1I2CObj.writeBuffer[sercom1I2CObj.writeCount++];

                        /* Wait for synchronization */
                            while((SERCOM1_REGS->I2CM.SERCOM_SYNCBUSY) != 0U)
                            {
                                /* Do nothing */
                            }
                    }

                    break;

                case SERCOM_I2C_STATE_TRANSFER_READ:

                    if(sercom1I2CObj.readCount == (sercom1I2CObj.readSize - 1U))
                    {
                        /* Set NACK and send stop condition to the slave from master */
                        SERCOM1_REGS->I2CM.SERCOM_CTRLB |= SERCOM_I2CM_CTRLB_ACKACT_Msk | SERCOM_I2CM_CTRLB_CMD(3UL);

                        /* Wait for synchronization */
                        while((SERCOM1_REGS->I2CM.SERCOM_SYNCBUSY) != 0U)
                        {
                            /* Do nothing */
                        }

                        sercom1I2CObj.state = SERCOM_I2C_STATE_TRANSFER_DONE;
                    }

                    /* Wait for synchronization */
                        while((SERCOM1_REGS->I2CM.SERCOM_SYNCBUSY) != 0U)
                        {
                            /* Do nothing */
                        }

                    /* Read the received data */
                    sercom1I2CObj.readBuffer[sercom1I2CObj.readCount++] = SERCOM1_REGS->I2CM.SERCOM_DATA;


                    break;

                default:

                    /* Do nothing */
                    break;
            }
        }

        /* Error Status */
        if(sercom1I2CObj.state == SERCOM_I2C_STATE_ERROR)
        {
            /* Reset the PLib objects and Interrupts */
            sercom1I2CObj.state = SERCOM_I2C_STATE_IDLE;

            /* Generate STOP condition */
            SERCOM1_REGS->I2CM.SERCOM_CTRLB |= SERCOM_I2CM_CTRLB_CMD(3UL);

            /* Wait for synchronization */
            while((SERCOM1_REGS->I2CM.SERCOM_SYNCBUSY) != 0U)
            {
                /* Do nothing */
            }


            SERCOM1_REGS->I2CM.SERCOM_INTFLAG = (uint8_t)SERCOM_I2CM_INTFLAG_Msk;

            if (sercom1I2CObj.callback != NULL)
            {
                sercom1I2CObj.callback(sercom1I2CObj.context);
            }
        }
        /* Transfer Complete */
        else if(sercom1I2CObj.state == SERCOM_I2C_STATE_TRANSFER_DONE)
        {
            /* Reset the PLib objects and interrupts */
            sercom1I2CObj.state = SERCOM_I2C_STATE_IDLE;
            sercom1I2CObj.error = SERCOM_I2C_ERROR_NONE;

            SERCOM1_REGS->I2CM.SERCOM_INTFLAG = (uint8_t)SERCOM_I2CM_INTFLAG_Msk;

            /* Wait for the NAK and STOP bit to be transmitted out and I2C state machine to rest in IDLE state */
            while((SERCOM1_REGS->I2CM.SERCOM_STATUS & SERCOM_I2CM_STATUS_BUSSTATE_Msk) != SERCOM_I2CM_STATUS_BUSSTATE(0x01UL))
            {
                /* Do nothing */
            }

            if(sercom1I2CObj.callback != NULL)
            {
                sercom1I2CObj.callback(sercom1I2CObj.context);
            }

        }
        else
        {
            /* Do nothing */
        }
    }

    return;
}
